arno6410/RoboGraphx/gcode/1074641-200.png

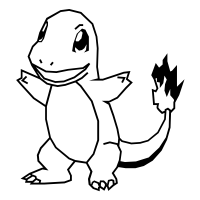
gcode/1074641-200.png
